EngineersNeedArt/Anna-Analog-Computer/Anna MAIN Pixie/AnnaMAINCode/SpriteUtils.h

// =============================================================================
//                                SpriteUtils.h
// =============================================================================

#pragma once


#include <stdint.h>
#include <stdbool.h>


#ifdef __cplusplus
extern "C" {
#endif


void fadeSpriteGreen (TFT_eSprite *sprite);


#ifdef __cplusplus
}
#endif
